ioquatix/hanging-door-roller/photos/IMG_7890.jpg

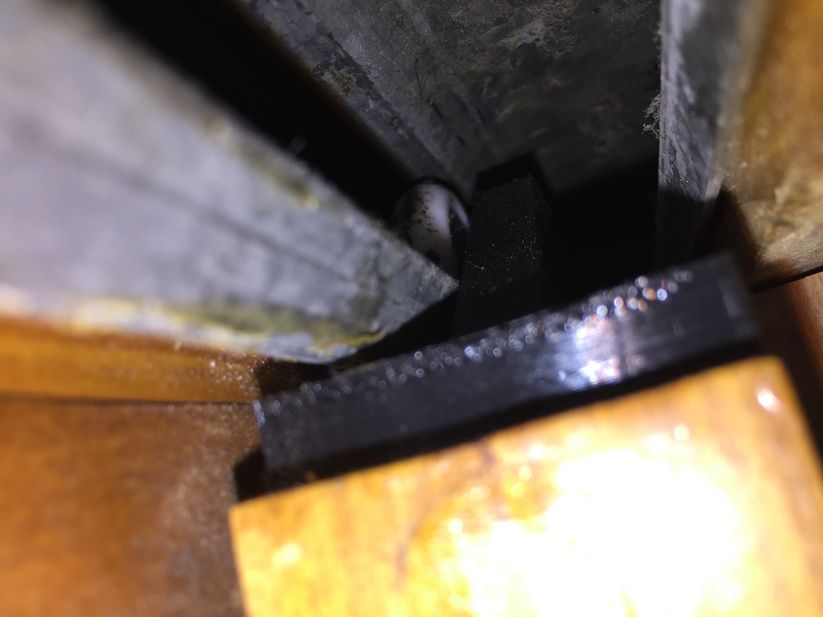
photos/IMG_7890.jpg
