ioquatix/hanging-door-roller/photos/IMG_7891.jpg

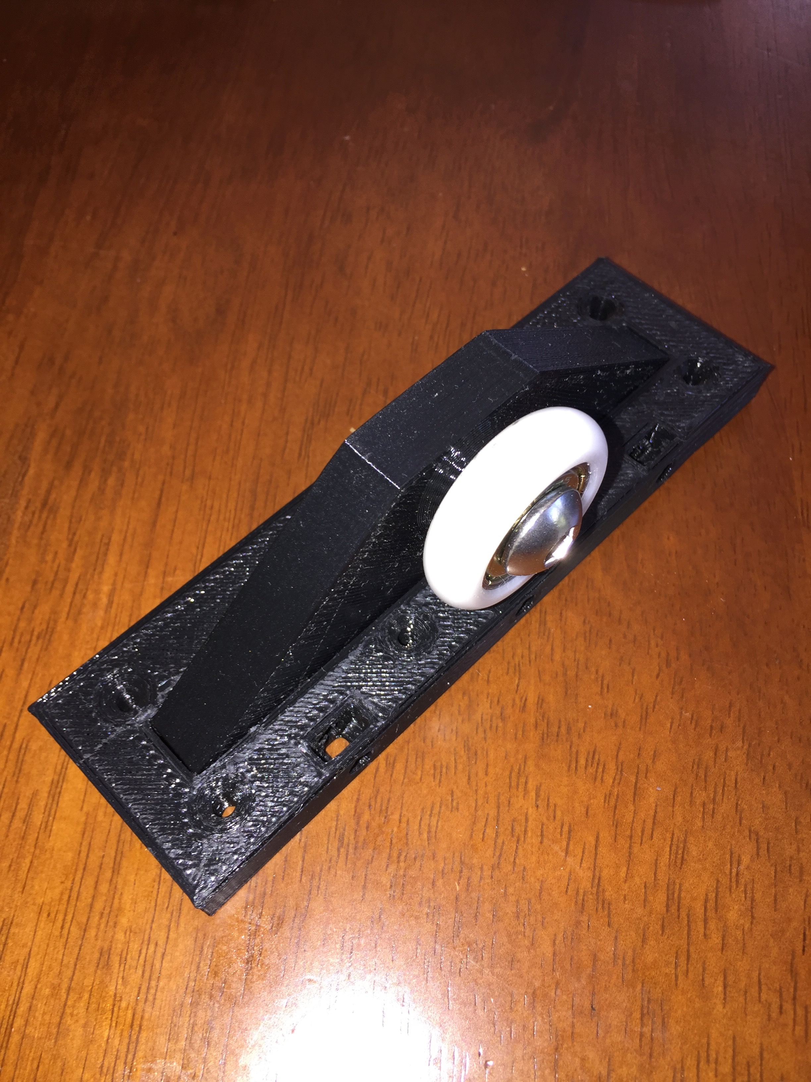
photos/IMG_7891.jpg
