ioquatix/hanging-door-roller/photos/IMG_7895.jpg

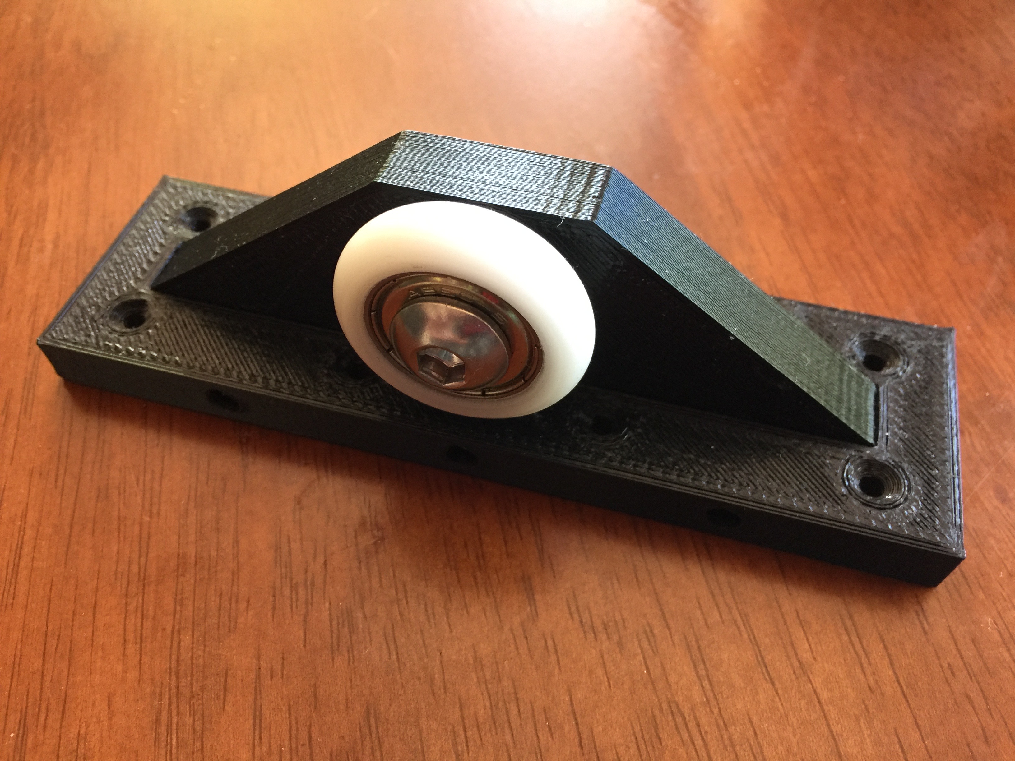
photos/IMG_7895.jpg
